JeremyLakeyJr/mesh-phone/hardware/handset-rev-a/generated/charge-inhibit-bom.csv

ref | value | mpn | footprint | role
Q8 | AO3400A | AO3400A | Package_TO_SOT_SMD:SOT-23 | Second series CE sink; default OFF during STM32 reset
R79 | 4.7k 1% | RC0402FR-074K7L | Resistor_SMD:R_0402_1005Metric | Local gate pull-down; not on the I2C bus
