JeremyLakeyJr/mesh-phone/mechanical/handset/exports/visual_ball.stl

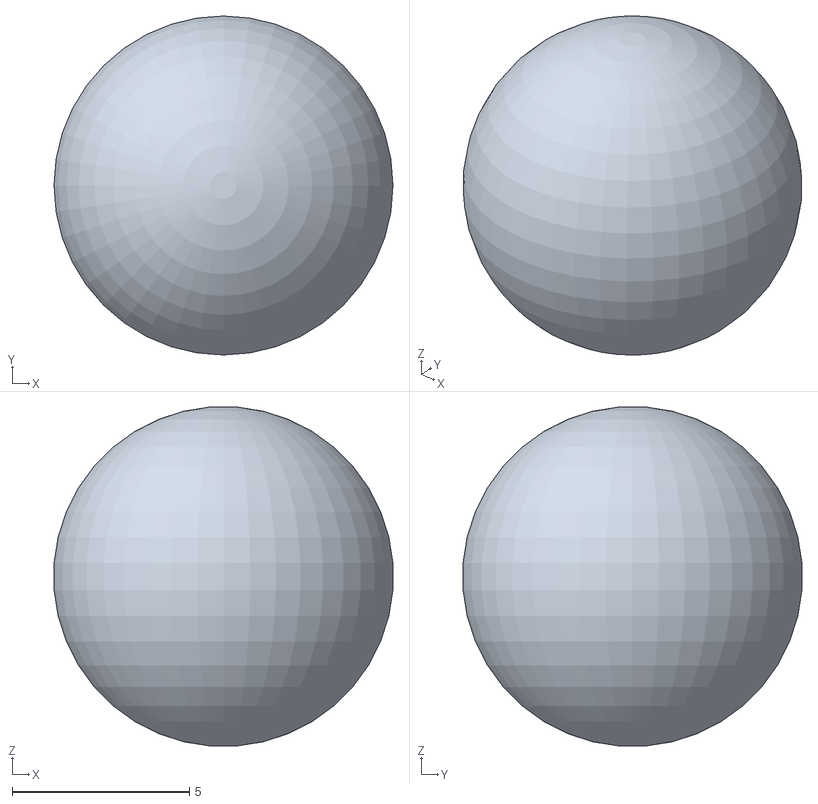
[picture p20: CAD file, 2026-09-21]
mechanical/handset/exports/visual_ball.stl
9.57 x 9.57 x 9.57
