JeremyLakeyJr/mesh-phone/mechanical/handset/exports/visual_screws.stl

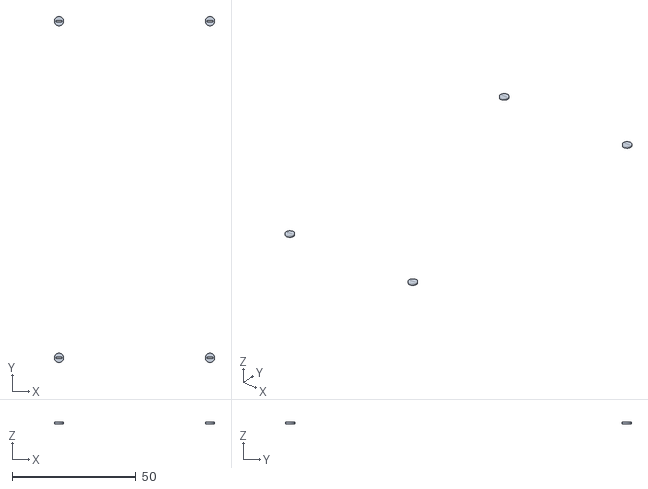
[picture p21: CAD file, 2026-09-21]
mechanical/handset/exports/visual_screws.stl
64.8 x 139.8 x 0.8
