JeremyLakeyJr/mesh-phone/mechanical/enclosure/pcb_geometry.scad

// Generated by scripts/enclosure_geometry.py; KiCad Y is inverted.
// PCB SHA256: 2a6ce225913ce72fe58441bef94259fdaef00b3df95e95820e0076893125d572
pcb_w = 87.0;
pcb_h = 154.0;
mounts = [[-40.5, 74.0], [40.5, 74.0], [-40.5, -74.0], [40.5, -74.0]];
keys = [[-22.05, -32.2], [-8.05, -32.2], [5.95, -32.2], [19.95, -32.2], [-22.05, -44.2], [-8.05, -44.2], [5.95, -44.2], [19.95, -44.2], [-22.05, -56.2], [-8.05, -56.2], [5.95, -56.2], [19.95, -56.2], [-22.05, -68.2], [-8.05, -68.2], [5.95, -68.2], [19.95, -68.2]];
usb = [39.25, 31.25];
power = [39.5, 43.0];
expansion = [-3.0, -10.0];
